tskauli/MorsePaddles/DSC04379_cr_exp.JPG

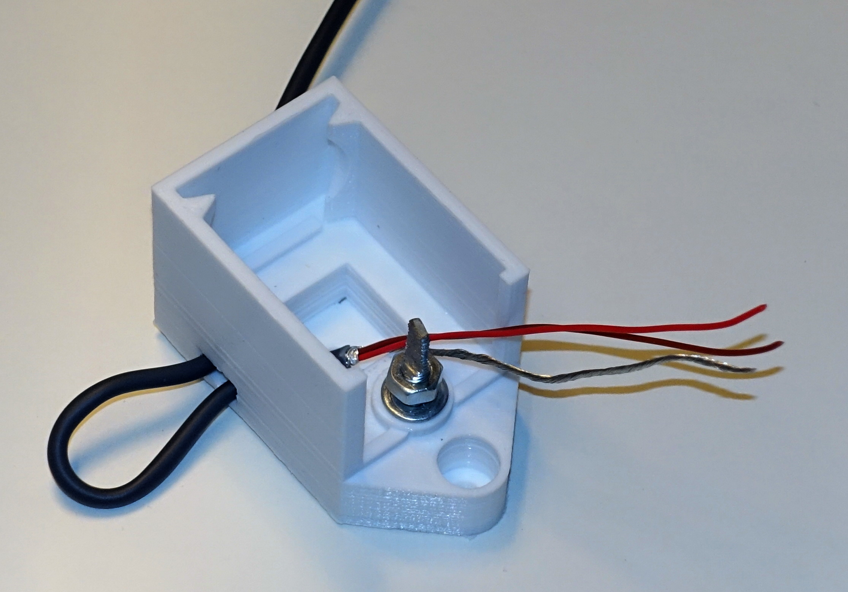
DSC04379_cr_exp.JPG
