tskauli/MorsePaddles/DSC04383_cr_exp.jpg

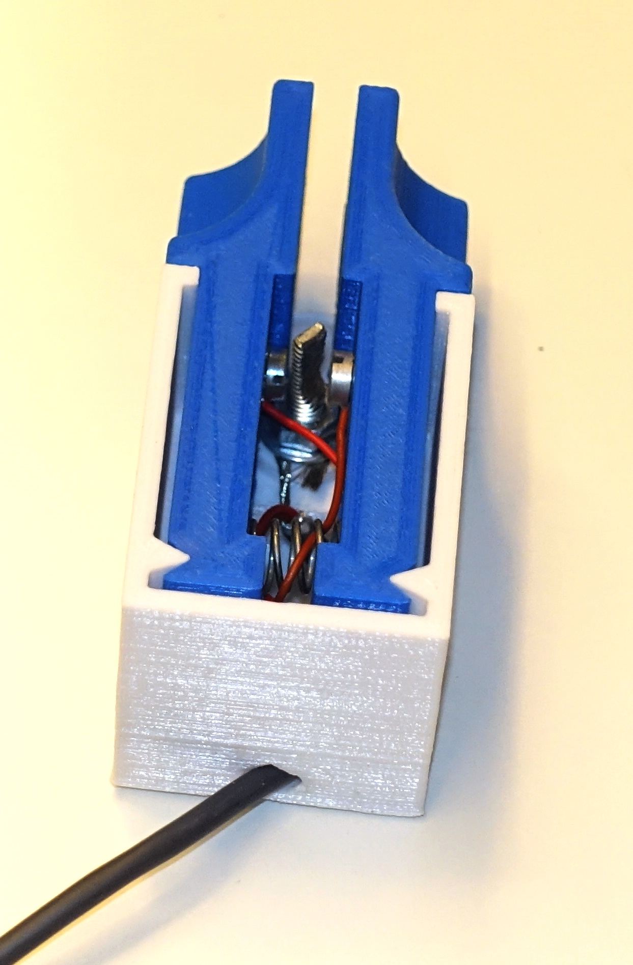
DSC04383_cr_exp.jpg
